TensorFleet/koyomi-lvds-hat/fab/r2.7-compact-rgb-production-jlc-candidate/renders/perspective.png

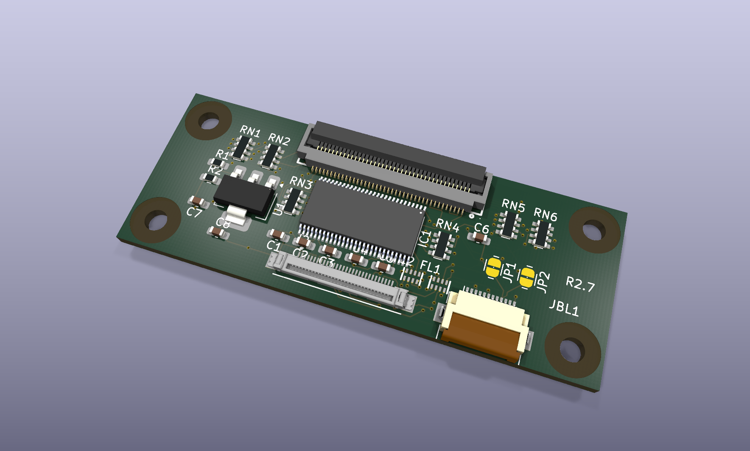
fab/r2.7-compact-rgb-production-jlc-candidate/renders/perspective.png
