TensorFleet/koyomi-lvds-hat/fab/r2.7-compact-rgb-production-jlc-candidate/renders/side.png

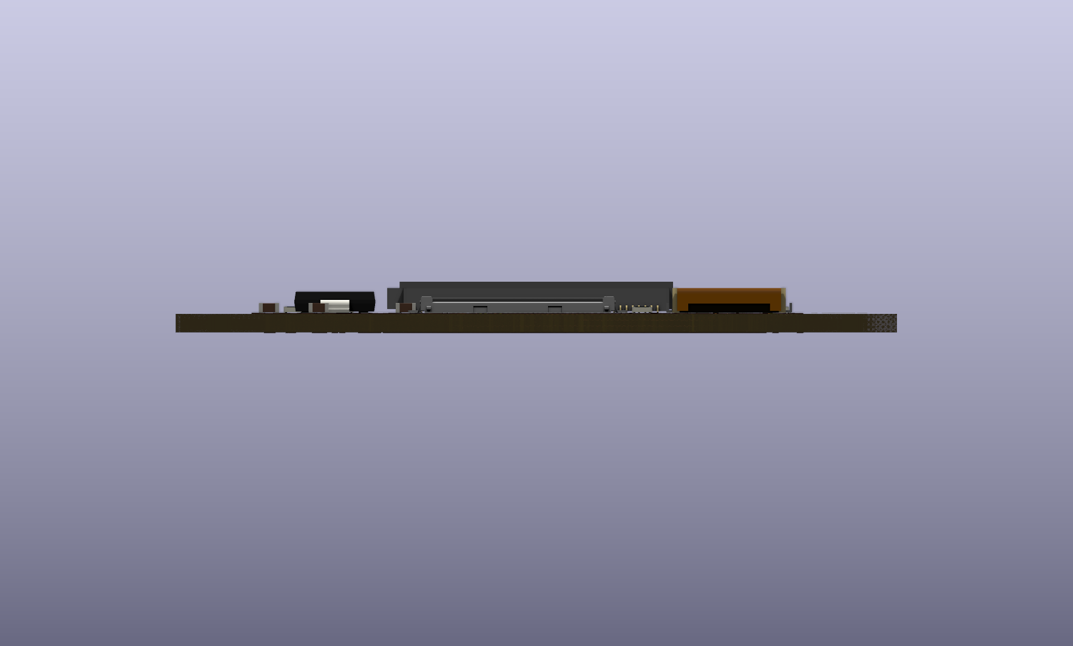
fab/r2.7-compact-rgb-production-jlc-candidate/renders/side.png
