TensorFleet/koyomi-lvds-hat/gpio-breakout-a2-b225/renders/top.png

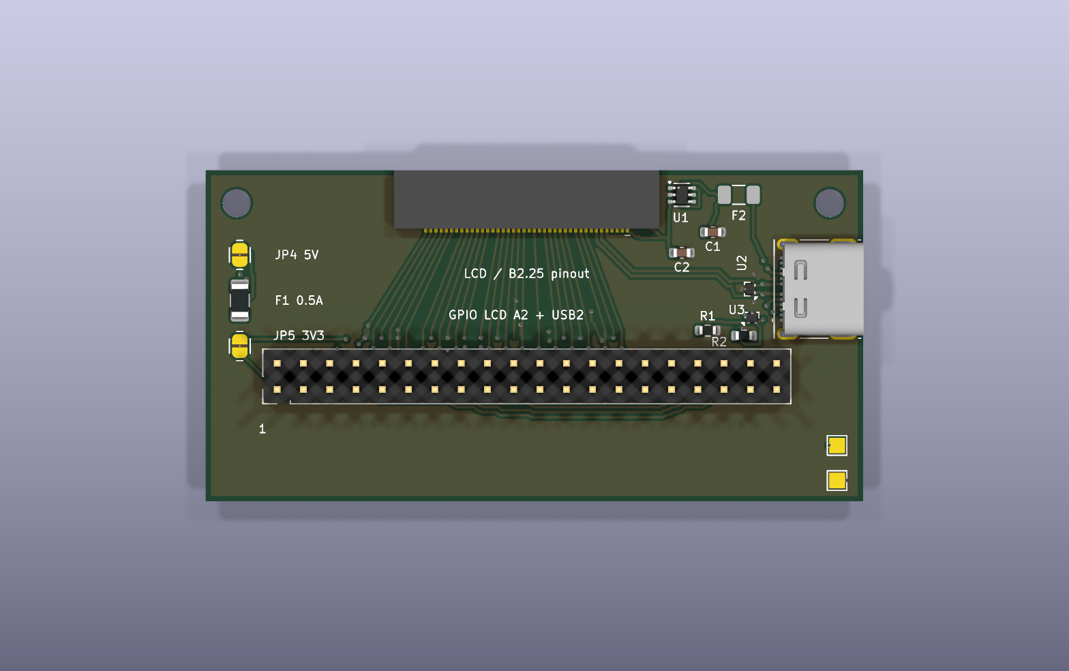
gpio-breakout-a2-b225/renders/top.png
