TensorFleet/koyomi-lvds-hat/gpio-breakout/renders/bottom.png

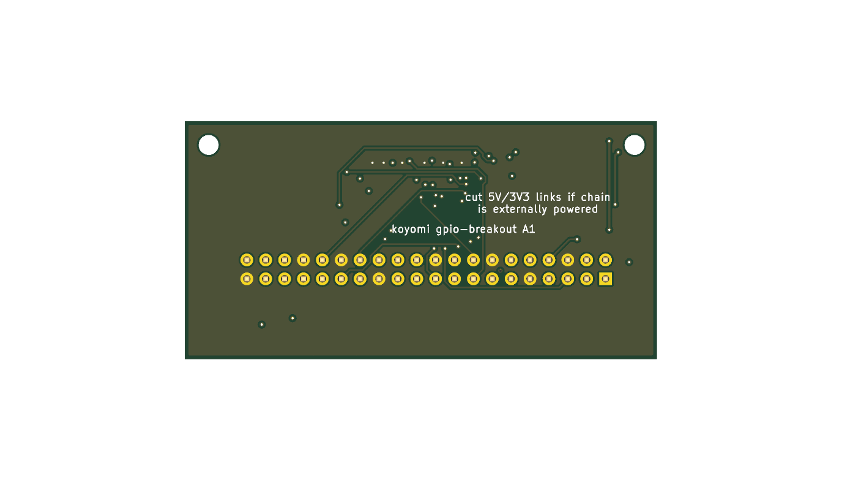
gpio-breakout/renders/bottom.png
