TensorFleet/koyomi-lvds-hat/gpio-breakout/renders/top.png

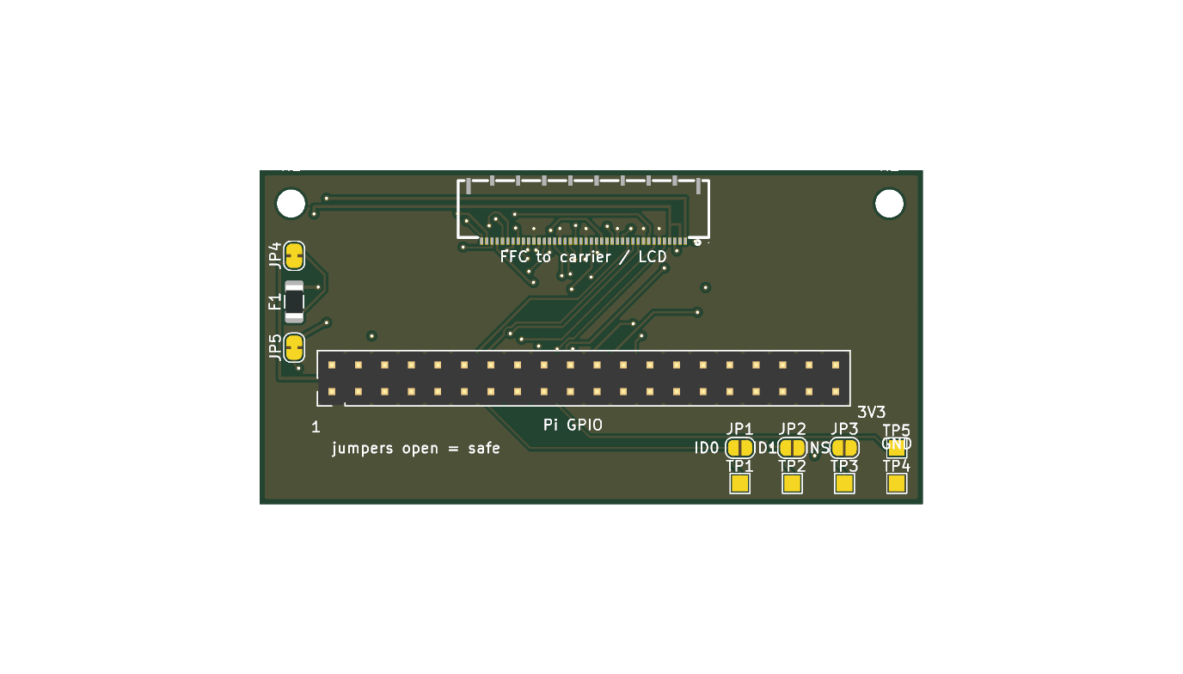
gpio-breakout/renders/top.png
